bripon76/SmithsSpeedo/Fotos/IMG_3480.jpg

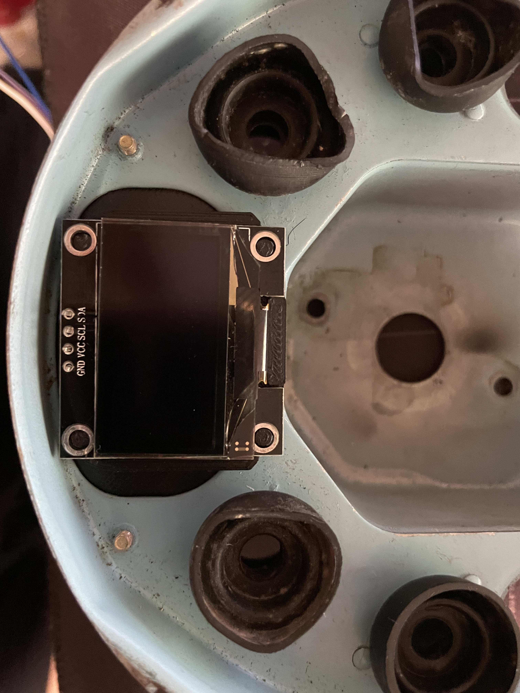
Fotos/IMG_3480.jpg
