bripon76/SmithsSpeedo/Fotos/IMG_3481.jpg

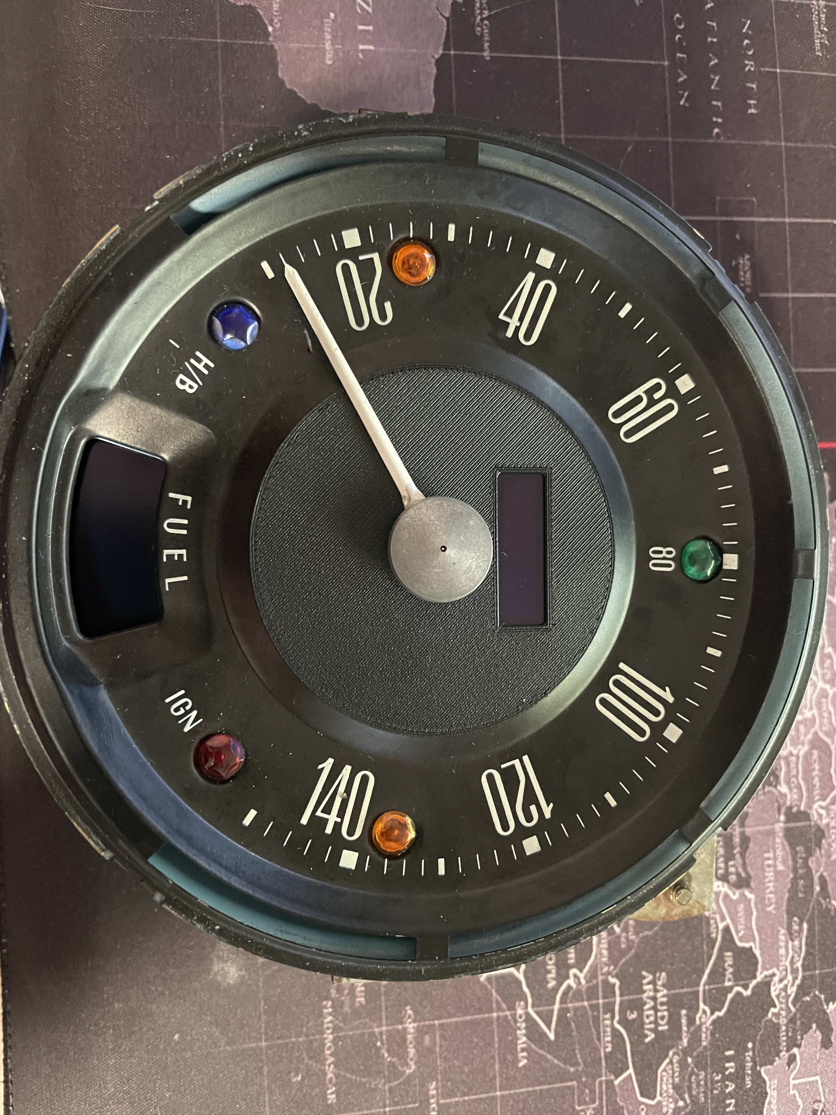
Fotos/IMG_3481.jpg
